way5/upgrading-classic-apples/models/macintosh plus/cooling fan/plus_fan_sprtpad_top.stl

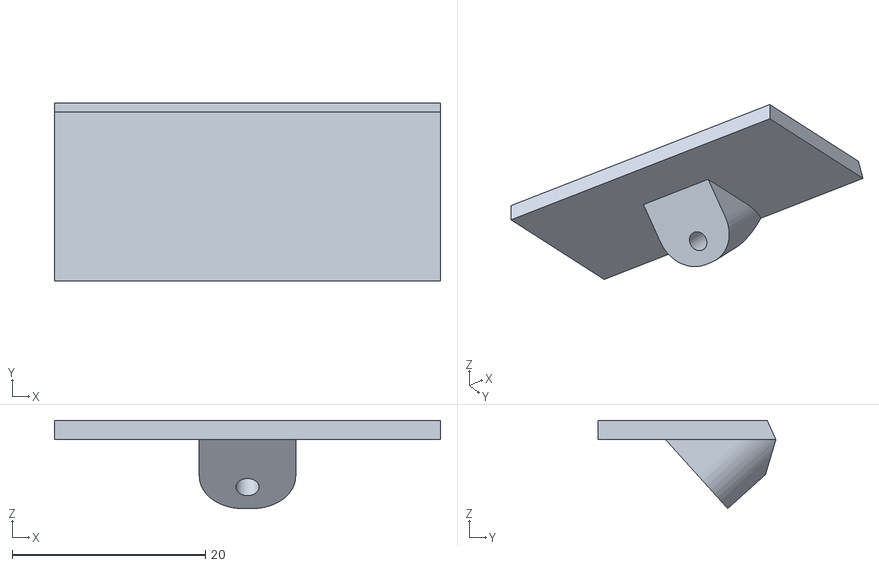
[picture p56: CAD file, 2023-07-06]
models/macintosh plus/cooling fan/plus_fan_sprtpad_top.stl
40.0 x 18.4 x 9.14
