way5/upgrading-classic-apples/models/sony MP-F75W/knob.stl

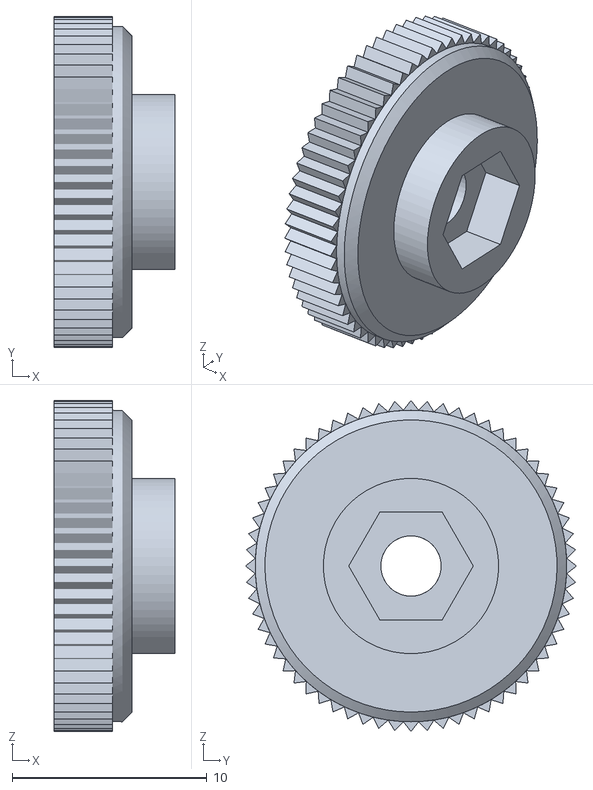
[picture p57: CAD file, 2023-07-06]
models/sony MP-F75W/knob.stl
6.20 x 17.0 x 17.0
